Ammar-Bin-Amir/Poultry_Bot/IoT_Monitoring_System/Display_Unit/Nextion_HMI_Display_for_1st_Milestone/Dashboard_Background_5.jpeg

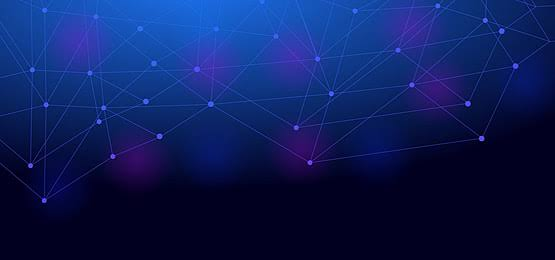
IoT_Monitoring_System/Display_Unit/Nextion_HMI_Display_for_1st_Milestone/Dashboard_Background_5.jpeg
