Ammar-Bin-Amir/Poultry_Bot/IoT_Monitoring_System/Display_Unit/Nextion_HMI_Display_for_2nd_Milestone/Background_2.jpeg

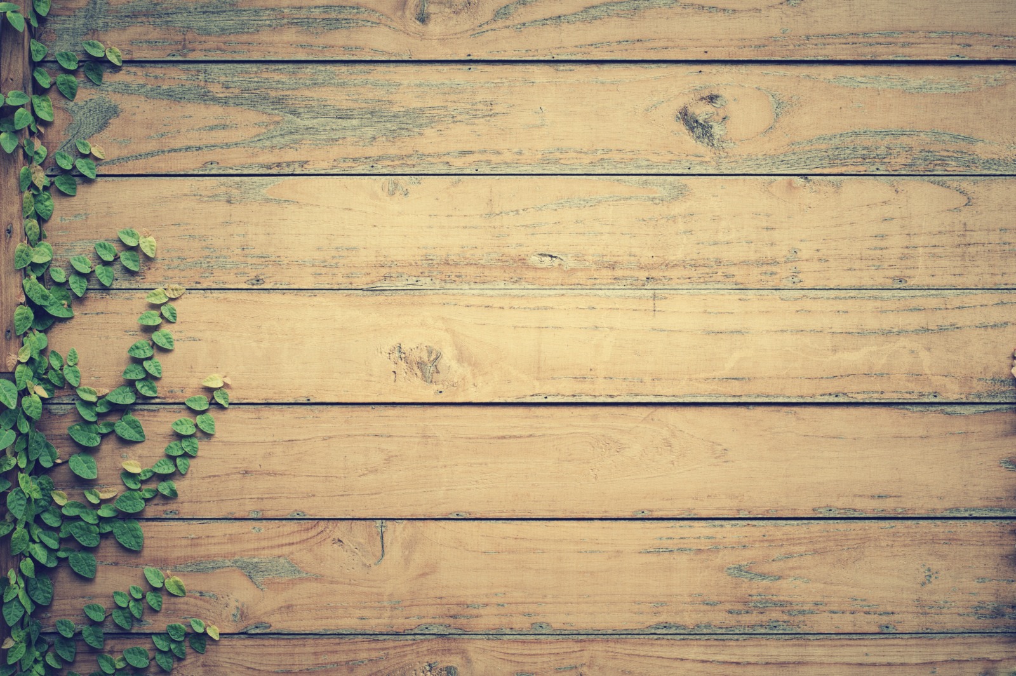
IoT_Monitoring_System/Display_Unit/Nextion_HMI_Display_for_2nd_Milestone/Background_2.jpeg
