Ammar-Bin-Amir/Poultry_Bot/IoT_Monitoring_System/Display_Unit/Nextion_HMI_Display_for_3rd_Milestone/Background_and_Gauge_300px_V1.png

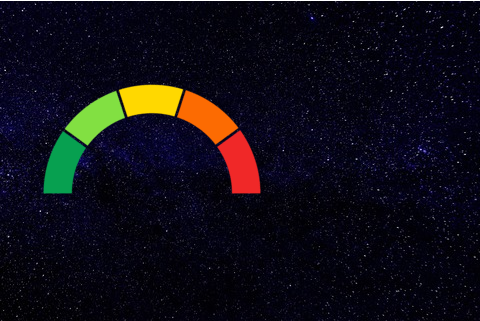
IoT_Monitoring_System/Display_Unit/Nextion_HMI_Display_for_3rd_Milestone/Background_and_Gauge_300px_V1.png
