Ammar-Bin-Amir/Poultry_Bot/IoT_Monitoring_System/Display_Unit/Nextion_HMI_Display_for_3rd_Milestone/Gauge Vertically Flipped Resized 300px.png

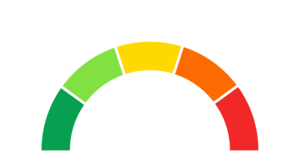
IoT_Monitoring_System/Display_Unit/Nextion_HMI_Display_for_3rd_Milestone/Gauge Vertically Flipped Resized 300px.png
