Ammar-Bin-Amir/Poultry_Bot/IoT_Monitoring_System/Remote_Control_App/Poultry_Bot_Remote_Control_App/Background_Vertical.jpeg

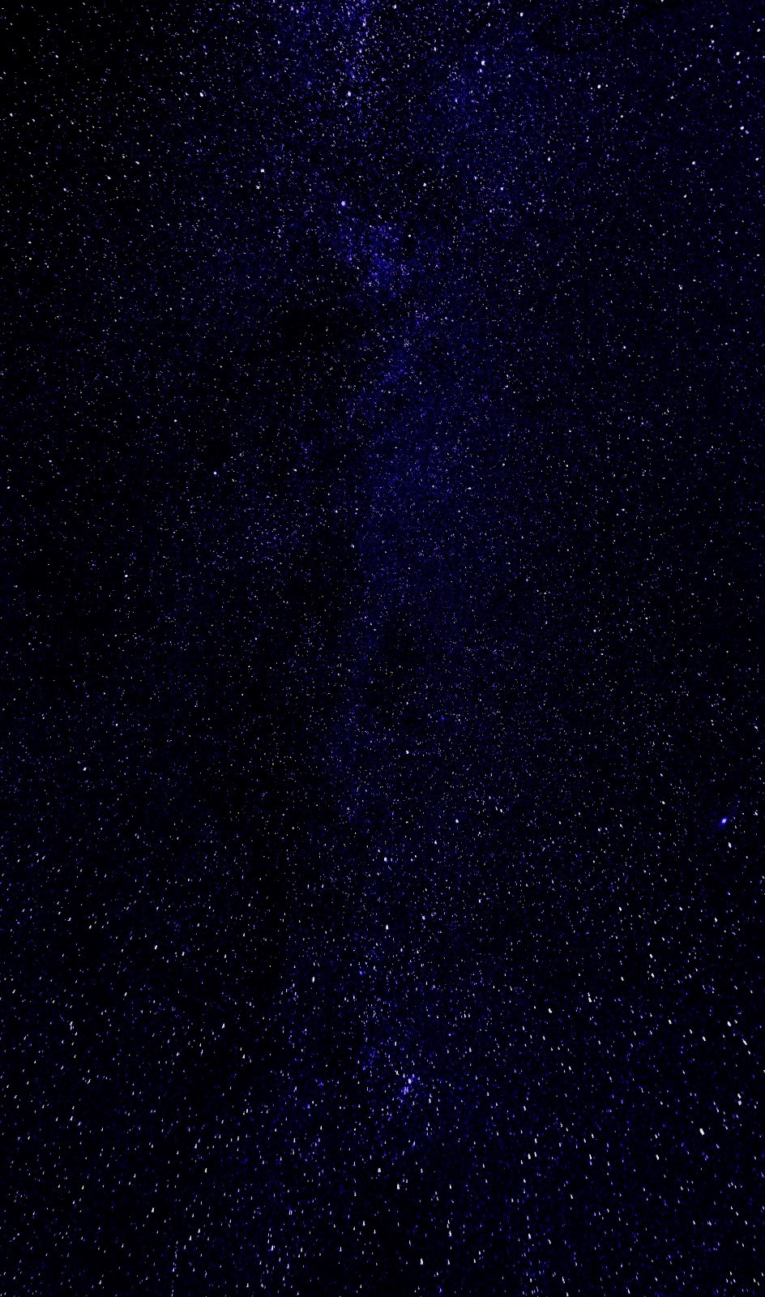
IoT_Monitoring_System/Remote_Control_App/Poultry_Bot_Remote_Control_App/Background_Vertical.jpeg
