Ammar-Bin-Amir/Poultry_Bot/IoT_Monitoring_System/Circuit/Circuit for 2nd Milestone/Design/Schematic.pdf

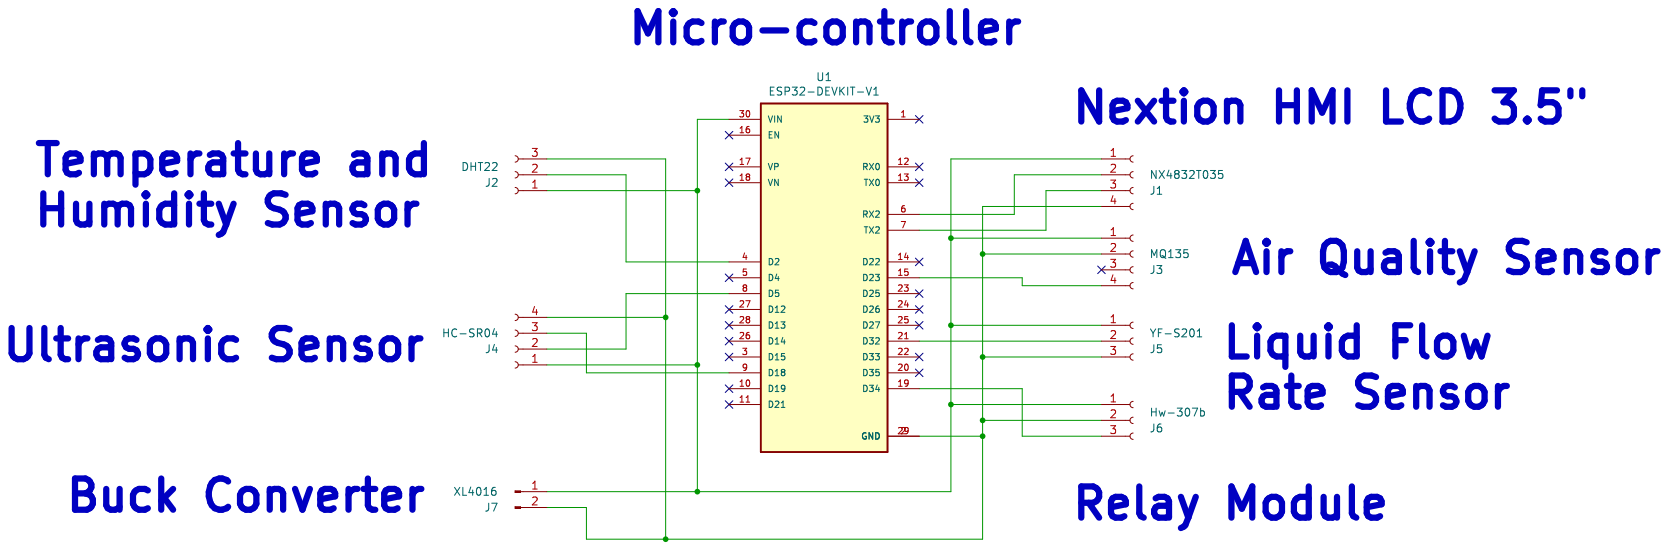
[picture p115: page 1]
