Ammar-Bin-Amir/Poultry_Bot/IoT_Monitoring_System/Circuit/Circuit for 2nd Milestone Updated/Layers/Print Files/Back Copper.pdf

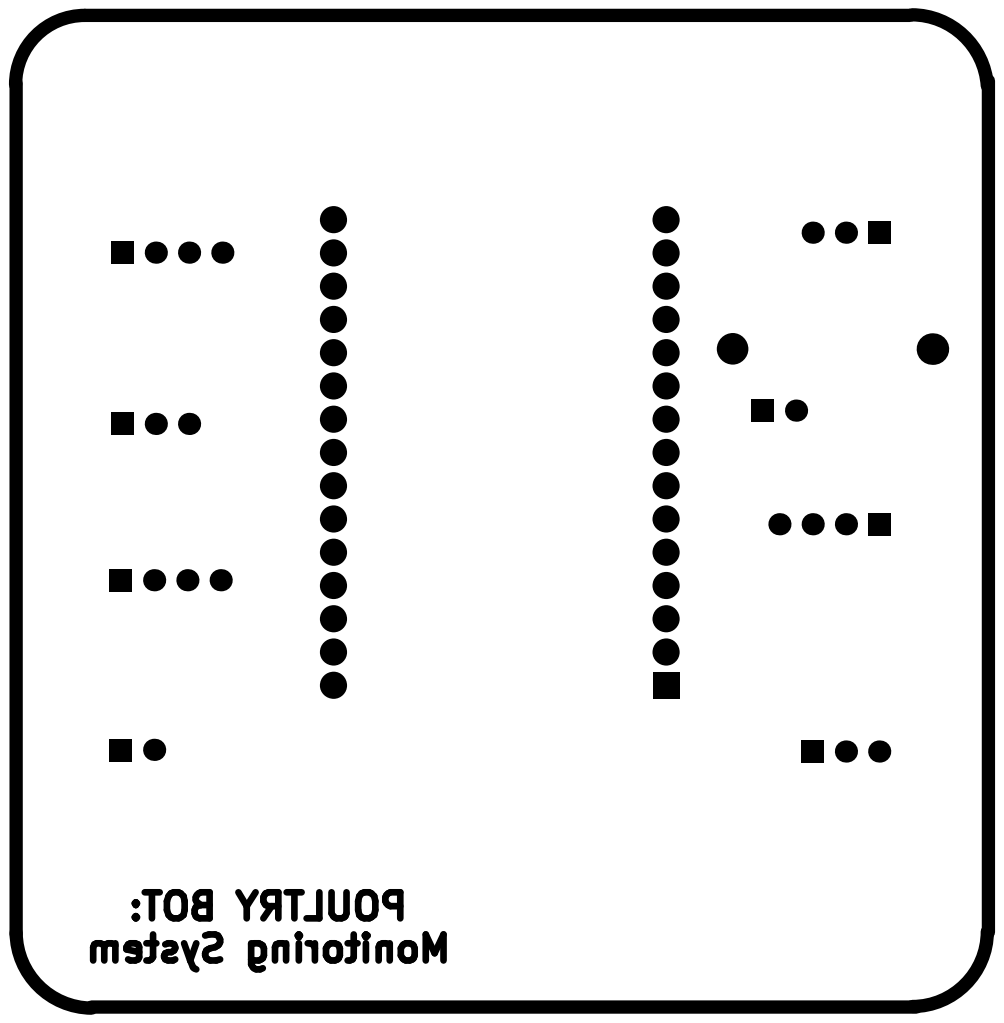
[picture p116: page 1]
