Ammar-Bin-Amir/Poultry_Bot/IoT_Monitoring_System/Circuit/Circuit for 2nd Milestone Updated/Layers/Print Files/Front Copper.pdf

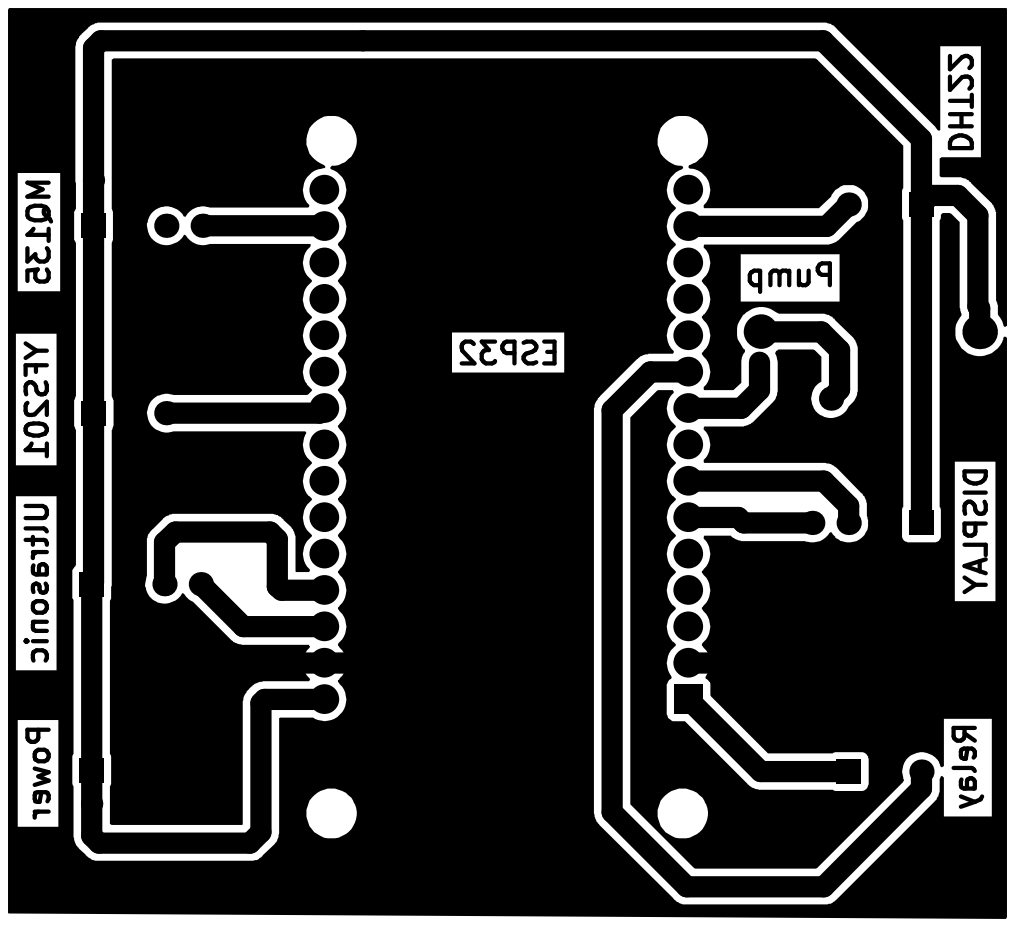
[picture p117: page 1]
