Ammar-Bin-Amir/Poultry_Bot/IoT_Monitoring_System/Circuit/Circuit for 2nd Milestone Updated/Layers/Print Files/Front Silkscreen.pdf

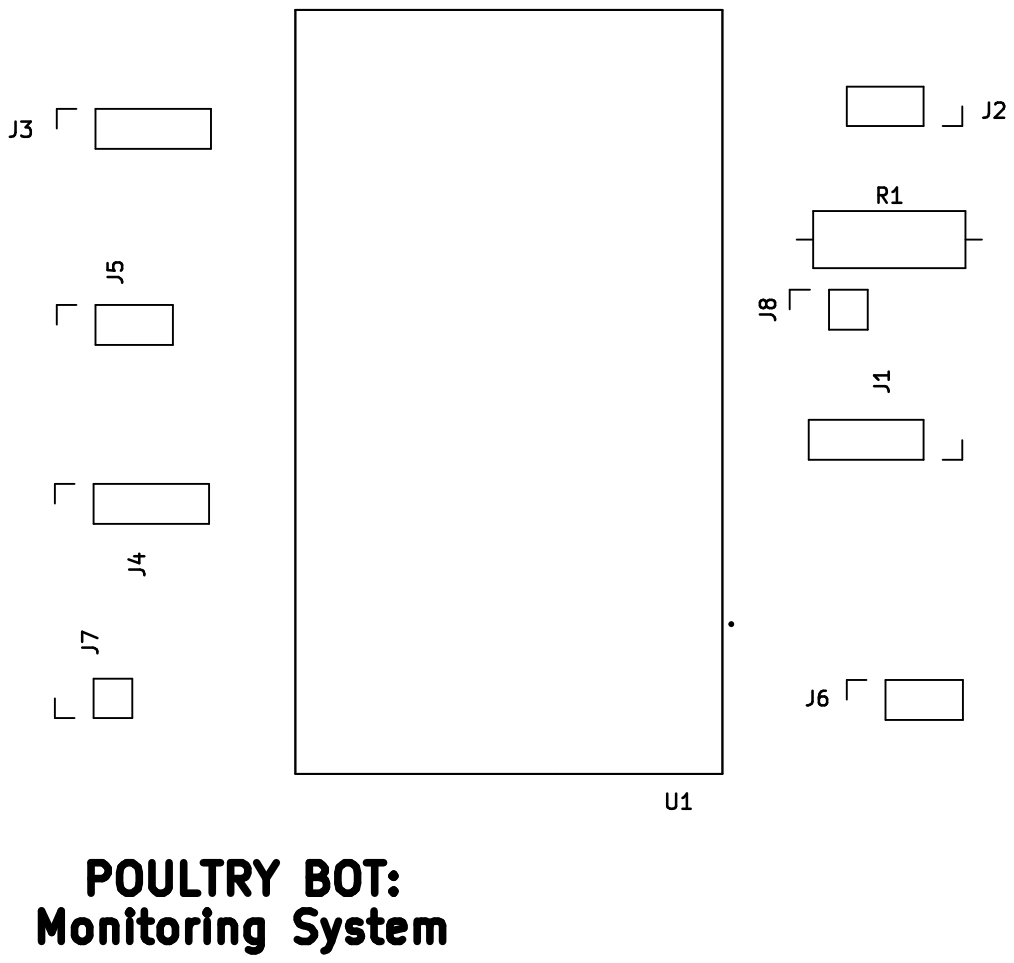
[picture p118: page 1]
