Ammar-Bin-Amir/Poultry_Bot/IoT_Monitoring_System/Circuit/Circuit for 2nd Milestone Updated/Layers/Print Files/Plated Through Hole.pdf

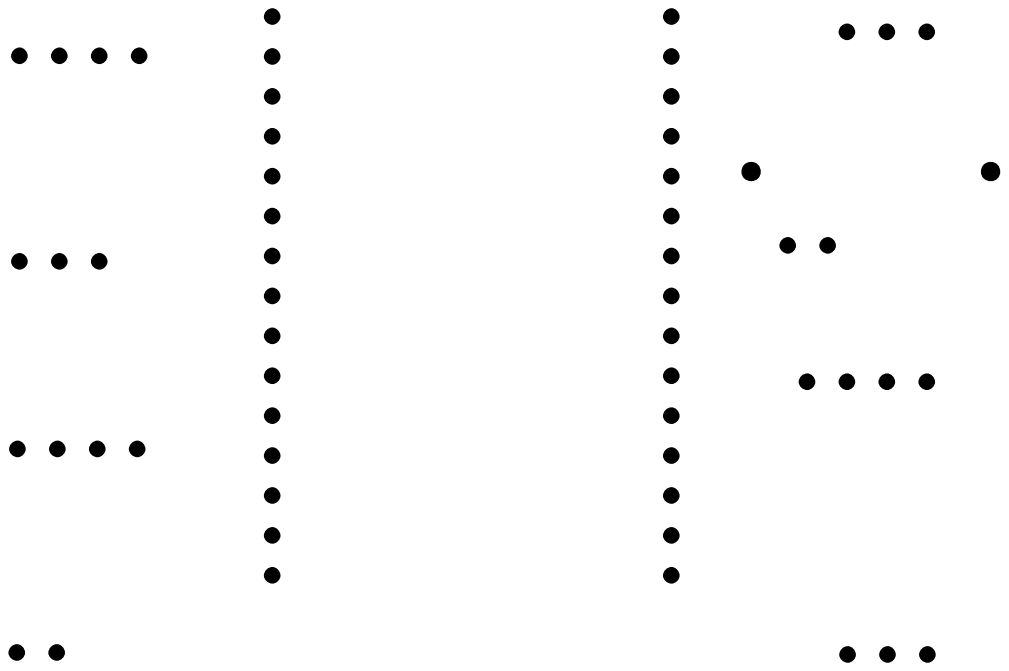
[picture p119: page 1]
