Ammar-Bin-Amir/Poultry_Bot/IoT_Monitoring_System/Circuit/Circuit for 3rd Milestone Complete/Layers/Print Files/Back Copper.pdf

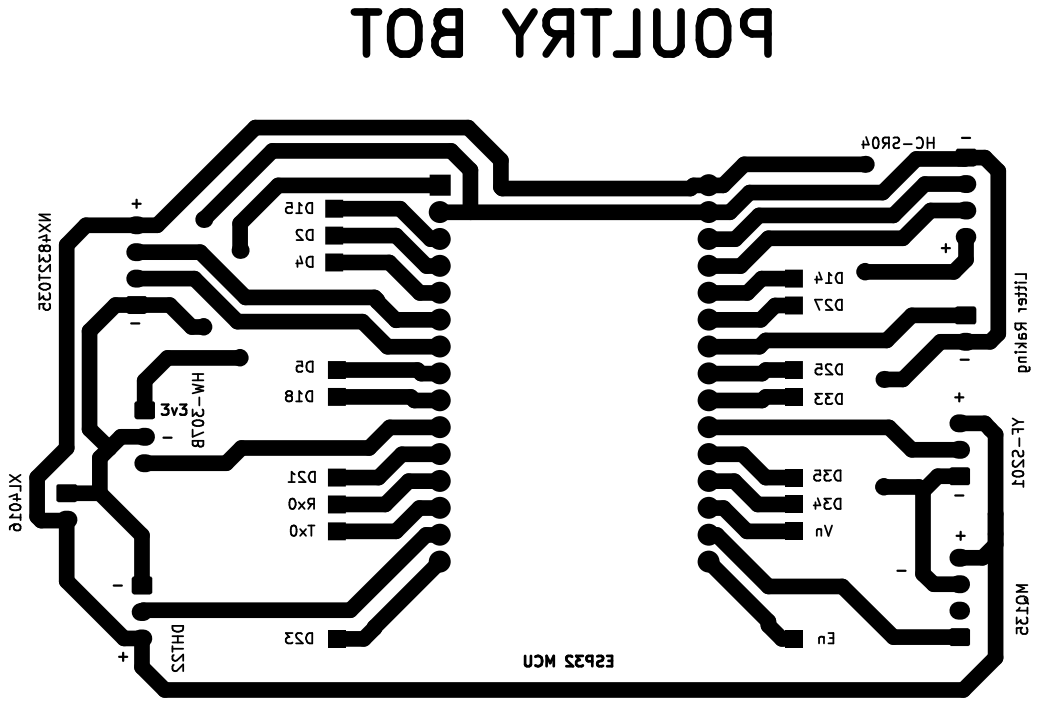
[picture p120: page 1]
