Ammar-Bin-Amir/Poultry_Bot/IoT_Monitoring_System/Circuit/Circuit for 3rd Milestone Complete/Layers/Print Files/Front Silkscreen.pdf

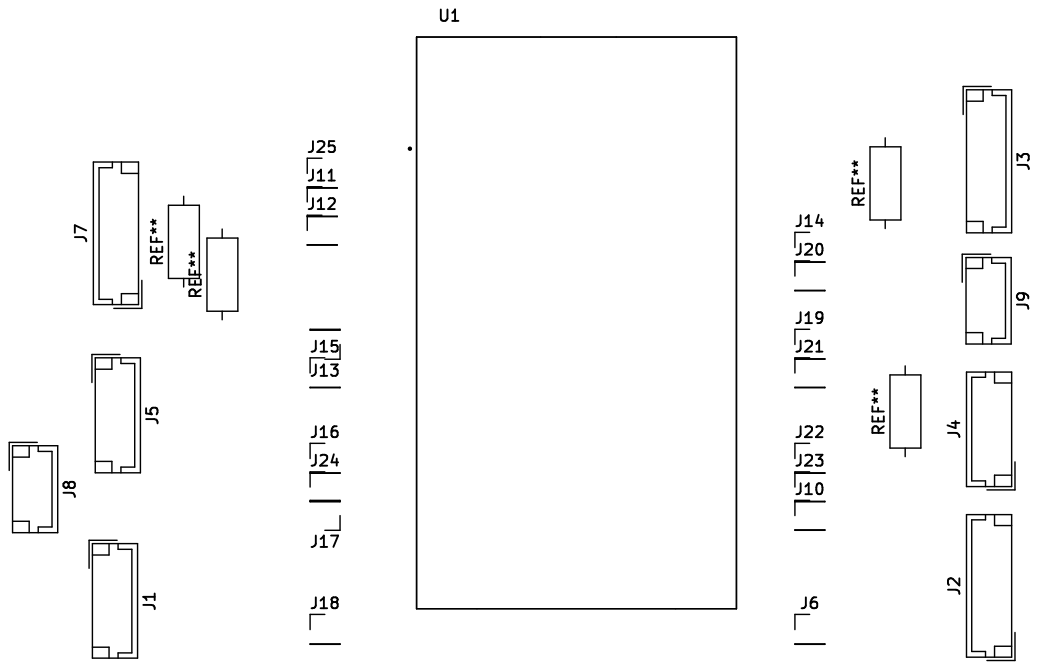
[picture p121: page 1]
