Ammar-Bin-Amir/Poultry_Bot/IoT_Monitoring_System/Circuit/Circuit for 3rd Milestone Complete/Layers/Print Files/Plated Through Hole.pdf

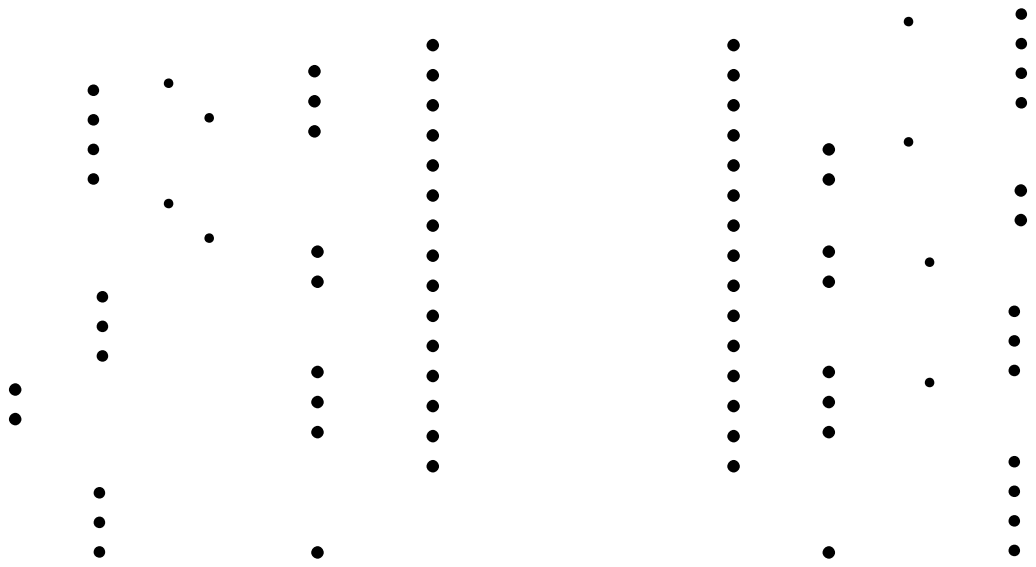
[picture p122: page 1]
