Ammar-Bin-Amir/Poultry_Bot/IoT_Monitoring_System/Circuit/Circuit for 1st Milestone/Layers/Print Files/Back Copper.pdf

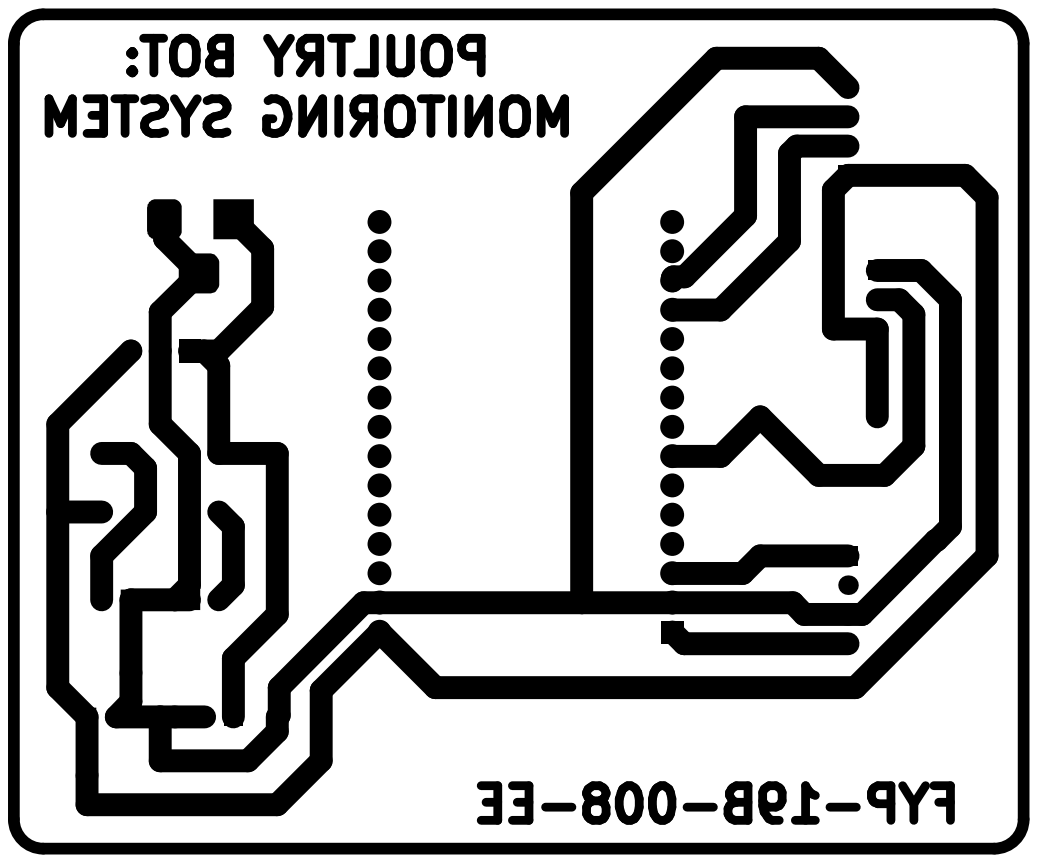
[picture p123: page 1]
