Ammar-Bin-Amir/Poultry_Bot/IoT_Monitoring_System/Circuit/Circuit for 1st Milestone/Layers/Print Files/Front Silkscreen.pdf

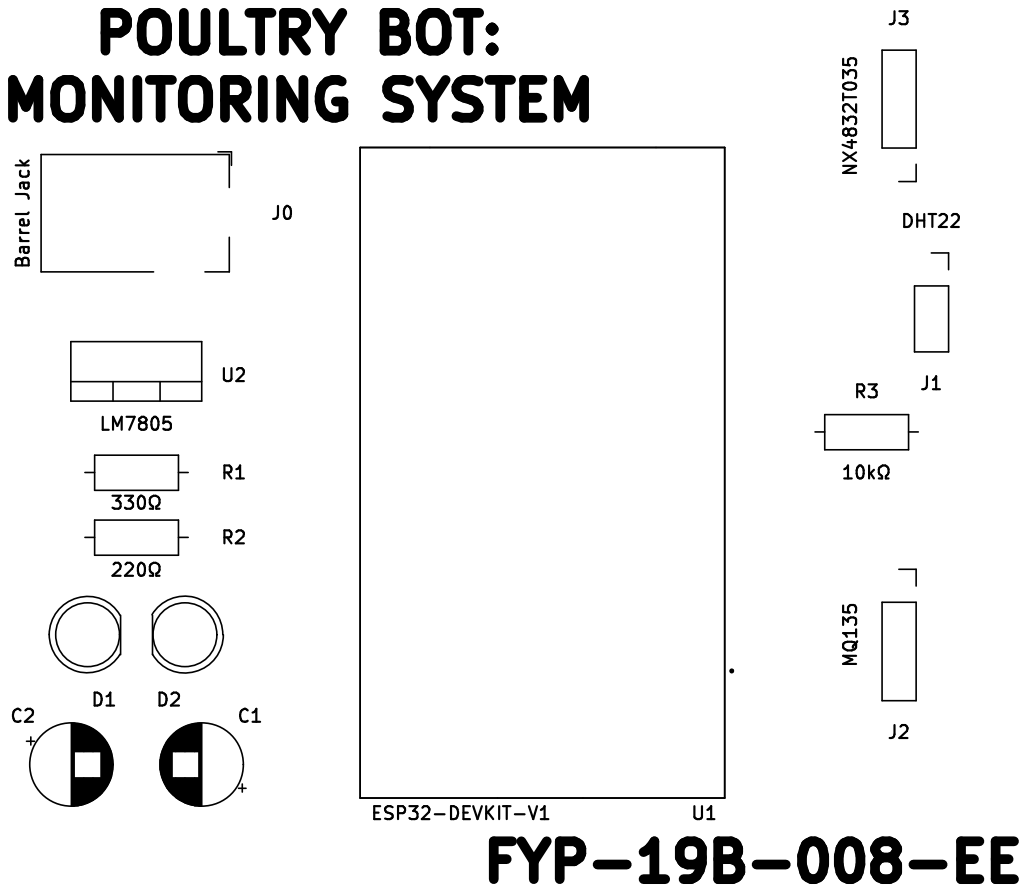
[picture p124: page 1]
