Ammar-Bin-Amir/Poultry_Bot/IoT_Monitoring_System/Circuit/Circuit for 1st Milestone/Layers/Print Files/Plated Through Hole.pdf

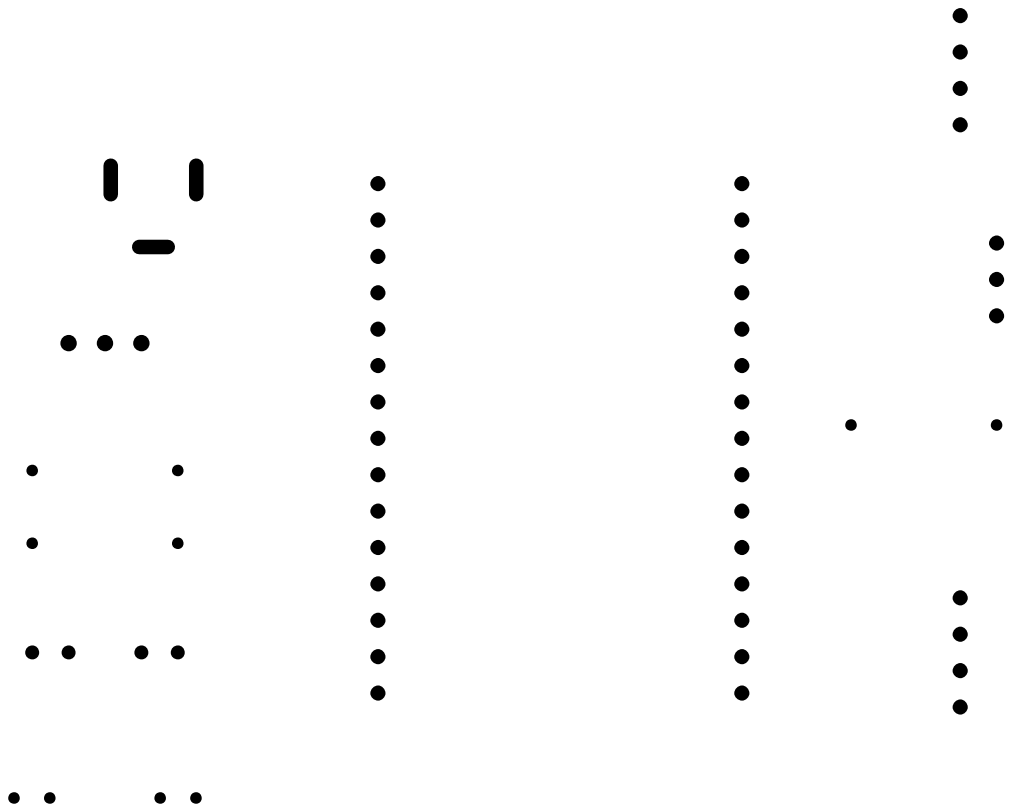
[picture p125: page 1]
