Ammar-Bin-Amir/Poultry_Bot/IoT_Monitoring_System/Circuit/Circuit for 2nd Milestone/Layers/Print Files/Back Copper.pdf

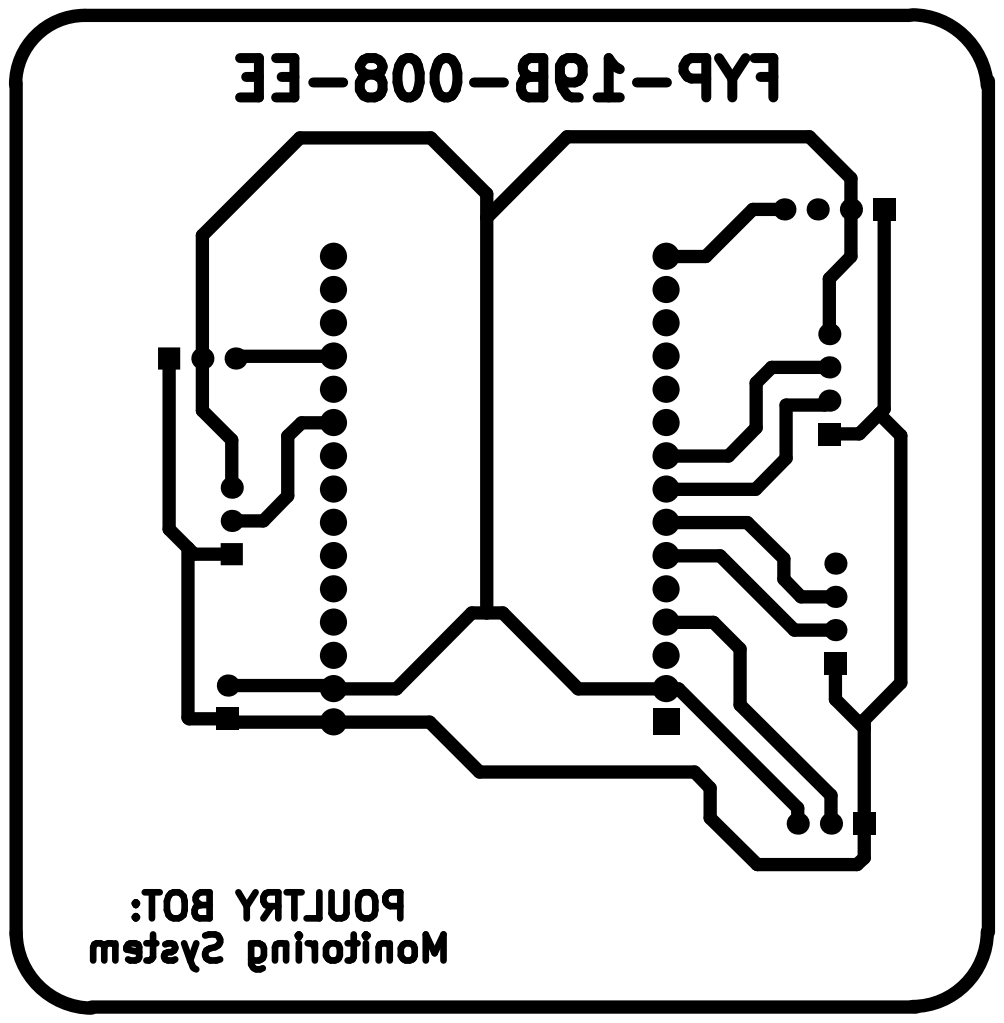
[picture p126: page 1]
