Ammar-Bin-Amir/Poultry_Bot/IoT_Monitoring_System/Circuit/Circuit for 2nd Milestone/Layers/Print Files/Front Silkscreen.pdf

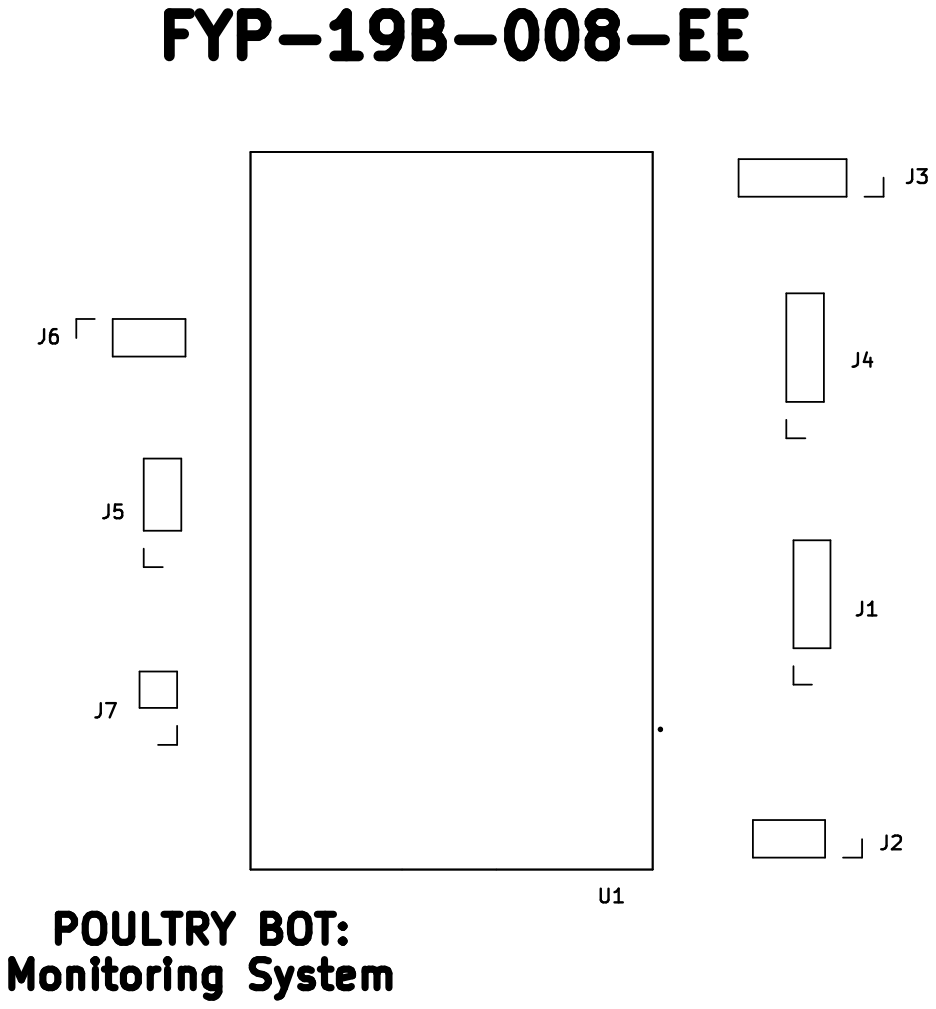
[picture p127: page 1]
