Ammar-Bin-Amir/Poultry_Bot/IoT_Monitoring_System/Circuit/Circuit for 2nd Milestone/Layers/Print Files/Plated Through Hole.pdf

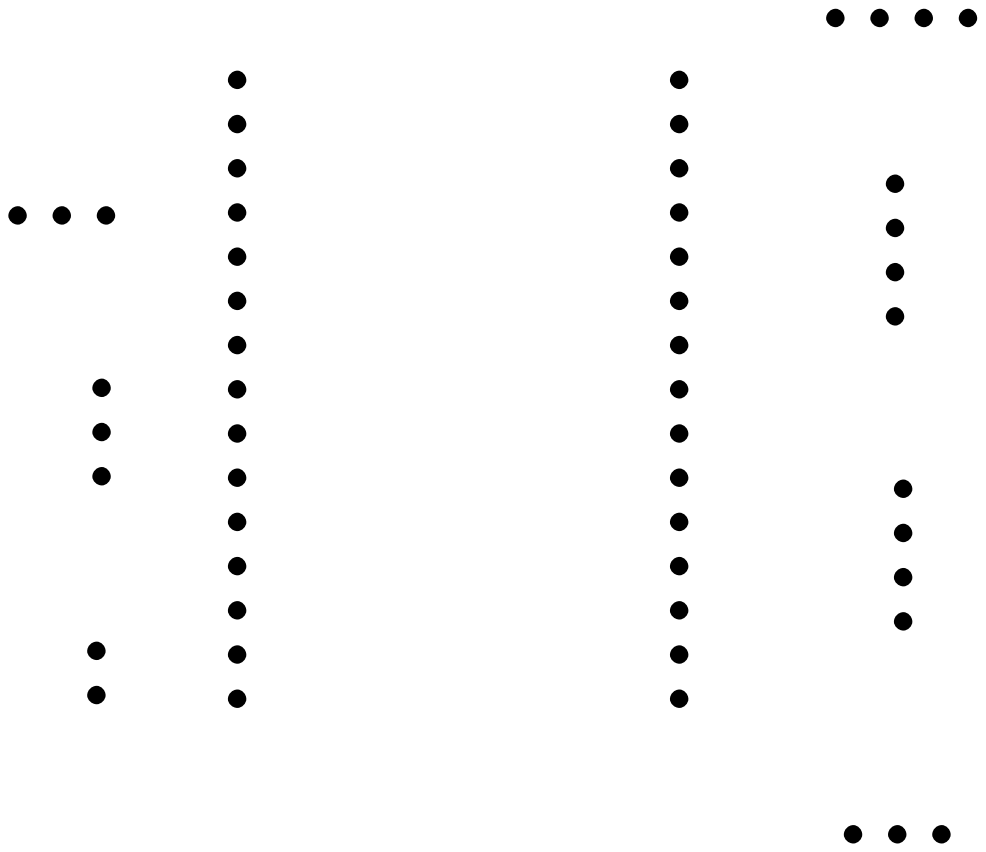
[picture p128: page 1]
